sincerelystepper/Smart-Penguin-Nest/Data Collection and Processing/Kicad Schematic/Kicad Schematic.kicad_sch

## KiCad design Data Collection and Processing/Kicad Schematic/Kicad Schematic.kicad_sch (2025-05-25)

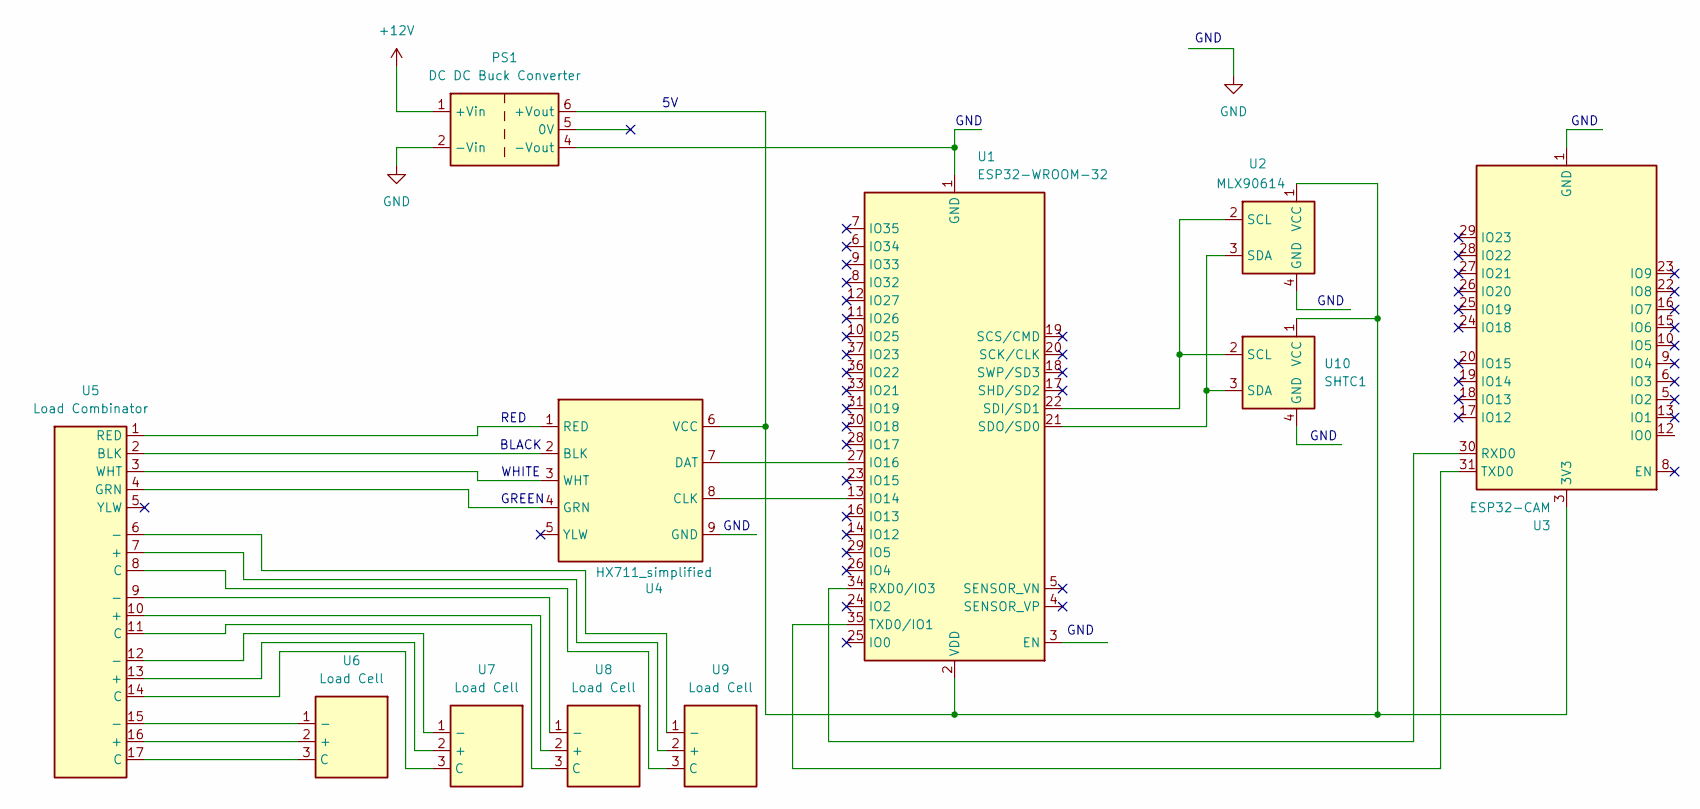
[picture p10: schematic Kicad Schematic.kicad_sch]

Parts:
PS1: DC DC Buck Converter; Converter_DCDC_XP_POWER-IAxxxxS_THT
U1: ESP32-WROOM-32
U2: MLX90614; Sensirion_DFN-4-1EP_2x2mm_P1mm_EP0.7x1.6mm
U3: ESP32-CAM; ESP32-C6-MINI-1
U4: HX711_simplified; SOP-16_3.9x9.9mm_P1.27mm
U5: Load Combinator; Sensirion_DFN-4-1EP_2x2mm_P1mm_EP0.7x1.6mm
U6, U7, U8, U9: Load Cell; Sensirion_DFN-4-1EP_2x2mm_P1mm_EP0.7x1.6mm
U10: SHTC1; Sensirion_DFN-4-1EP_2x2mm_P1mm_EP0.7x1.6mm

Connections:
+12V: PS1.1 (+Vin)
GND: PS1.2 (-Vin)
unnamed: PS1.4 (-Vout), U1.1 (GND), U1.15 (GND), U1.38 (GND), U1.39 (GND)
unnamed: PS1.6 (+Vout), U1.2 (VDD), U2.1 (VCC), U3.3 (3V3), U4.6 (VBG), U10.1 (VCC)
unnamed: U1.13 (IO14), U4.8 (CLK)
unnamed: U1.21 (SDO/SD0), U2.3 (SDA), U10.3 (SDA)
unnamed: U1.22 (SDI/SD1), U2.2 (SCL), U10.2 (SCL)
unnamed: U1.27 (IO16), U4.7 (DAT)
unnamed: U1.34 (RXD0/IO3), U3.30 (RXD0)
unnamed: U1.35 (TXD0/IO1), U3.31 (TXD0)
unnamed: U3.1 (GND), U3.2 (GND), U3.11 (GND), U3.14 (GND), U3.36 (GND), U3.37 (GND), U3.38 (GND), U3.39 (GND), U3.40 (GND), U3.41 (GND), U3.42 (GND), U3.43 (GND), U3.44 (GND), U3.45 (GND), U3.46 (GND), U3.47 (GND), U3.48 (GND), U3.49 (GND), U3.50 (GND), U3.51 (GND), U3.52 (GND), U3.53 (GND)
unnamed: U4.1 (RED), U5.1 (RED)
unnamed: U4.2 (BASE), U5.2 (BLK)
unnamed: U4.3 (WHT), U5.3 (WHT)
unnamed: U4.4 (GRN), U5.4 (GRN)
unnamed: U5.6 (-), U9.1 (-)
unnamed: U5.7 (+), U9.2 (+)
unnamed: U5.8 (C), U9.3 (C)
unnamed: U5.9 (-), U8.1 (-)
unnamed: U5.10 (+), U8.2 (+)
unnamed: U5.11 (C), U8.3 (C)
unnamed: U5.12 (-), U7.1 (-)
unnamed: U5.13 (+), U7.2 (+)
unnamed: U5.14 (C), U7.3 (C)
unnamed: U5.15 (-), U6.1 (-)
unnamed: U5.16 (+), U6.2 (+)
unnamed: U5.17 (C), U6.3 (C)

Notes on the sheet:
GND
BLACK
WHITE
RED
GREEN
